vad32m/OpenDcLoad/hw/analog_sim/load_frontend.cir

[Main]
FileType=CIR
Version=12.00
Program=Micro-Cap
Component Version=10.00
Shape Version=11.00
Screen=1680,1050
MCAPVersion=12.2.0.3
Key ID=Demo
NLCnt=155
TXCnt=8

[shapedef]
Name=Animated SPDT Switch
Animated SPDT Switch=0,0,48,16
Current=0,24,16,24
Current=0,-8,16,-8
Current=32,0,48,0

[shapedef]
Name=Animated SPST Switch
Animated SPST Switch=0,-8,48,8
Current=16,8,32,8

[shapedef]
Name=Comp6
Root="Plus.root",9,-12,0
Root="Minus.root",9,44,0
Line=16,48,16,26
Line=16,-16,16,5
Line=24,21,24,40
Line=24,40,56,40
Root="Opamp.root",-16,-8,0

[shapedef]
Name=DNMOS
Root="Mos2.root",0,0,0
Line=14,0,24,0
PolyClosed=3
PolyLine=17,0
PolyLine=20,-3
PolyLine=20,3

[shapedef]
Name=Ground
Line=0,0,12,0
Line=12,-8,12,8
Line=18,-4,18,4
Line=24,0,24,0

[shapedef]
Name=Minus.root
Line=-2,0,2,0

[shapedef]
Name=Mos2.root
Line=0,8,10,8
Line=10,-8,10,8
Line=14,-11,14,-5
Line=14,-3,14,3
Line=14,5,14,11
Line=14,-8,24,-8
Line=14,8,24,8
Line=24,0,24,24
Line=24,-8,24,-24
Current=32,-24,32,-16
Current=32,24,32,16
Current=0,0,8,0

[shapedef]
Name=Opamp5
Root="Opamp.root",0,0,0
Root="Plus.root",25,-4,0
Root="Minus.root",25,52,0
Line=32,56,32,34
Line=32,-8,32,13

[shapedef]
Name=Opamp.root
Line=0,48,6,48
Line=0,0,5,0
Line=6,-4,6,52
Line=6,-4,48,24
Line=6,52,48,24
Line=48,24,72,24
Line=10,12,14,12
Line=12,10,12,14
Line=10,36,14,36
Line=4,0,6,0

[shapedef]
Name=Plus.root
Line=-2,0,2,0
Line=0,-2,0,2

[shapedef]
Name=Pot
Line=0,0,12,0
Line=12,0,14,-4
Line=14,-4,18,4
Line=18,4,22,-4
Line=22,-4,26,4
Line=26,4,30,-4
Line=30,-4,34,4
Line=34,4,36,0
Line=36,0,48,0
PolyClosed=4
PolyLine=24,4
PolyLine=24,4
PolyLine=22,8
PolyLine=26,8
Line=24,8,24,16

[shapedef]
Name=Resistor
PolyOpen=12
PolyLine=0,0
PolyLine=0,0
PolyLine=12,0
PolyLine=14,-4
PolyLine=18,4
PolyLine=22,-4
PolyLine=26,4
PolyLine=30,-4
PolyLine=34,4
PolyLine=36,0
PolyLine=48,0
PolyLine=48,0
Current=32,8,16,8

[shapedef]
Name=SPICE_V
Root="Vsource.root",0,0,0

[shapedef]
Name=Tie
Line=0,0,7,0
Line=7,-8,7,8

[shapedef]
Name=Vsource.root
Line=0,0,12,0
Line=36,0,48,0
Ellipse=12,-12,36,12
FColor=None
Line=7,5,7,9
Root="Plus.root",41,7,0
Current=32,16,16,16

[compdef]
Name=Resistor
Definition=Resistor
Shape=Resistor
Mask=6913
Used=170
memo=Resistor
Label Offset=18,6,8,11
PinCnt=2
Pin="Plus",6,0,-10,-4
Pin="Minus",0,0,-14,-4

[compdef]
Name=Ground
Definition=Ground
Shape=Ground
Mask=1793
Used=277
memo=Ground
Label Offset=0,0,0,0
PinCnt=1
Pin="PinA",0,0,-3,-7

[compdef]
Name=Voltage Source
Definition=VSpice
Shape=SPICE_V
Mask=4865
Used=41
memo=Voltage Source
Label Offset=19,13,15,13
PinCnt=2
Pin="Plus",6,0,-5,-6
Pin="Minus",0,0,-20,-6

[compdef]
Name=Tie
Definition=Tie
Shape=Tie
Mask=5632
Used=9
memo=Ties two nodes together
Label Offset=11,-6,-6,8
PinCnt=1
Pin="PinA",0,0,-7,-9

[compdef]
Name=IRFP350
Definition=NMOS
Shape=DNMOS
Mask=4224
Used=1
memo=N-Channel Power MOSFET Vdss=400V Id=15A Rds=0.3ohm
Label Offset=29,-13,-5,26
PinCnt=4
Pin="Drain",3,-3,7,8
Pin="Gate",0,1,-19,-2
Pin="Source",3,3,6,12
Pin="Body",3,3,6,0
Power=180

[compdef]
Name=AD8628
Definition=Subckt
Shape=Opamp5
Mask=4224
Used=3
memo=Zero Drift, Single Supply, Rail-to-Rail I/O Opamp
Label Offset=51,31,-10,41
PinCnt=5
Pin="1",a,0,0,-3,-4
Pin="2",a,0,6,-3,18
Pin="99",a,4,-1,6,15
Pin="50",a,4,7,6,0
Pin="45",a,9,3,-3,-3

[compdef]
Name=INA214
Definition=Subckt
Shape=Comp6
Mask=4224
Used=2
memo=Voltage Output, High or Low Side Measurement, Bidirectional Zero Drift Series Current Shunt Monitor Gain=100
Link=http://www.ti.com/lit/ds/symlink/ina210.pdf
Label Offset=27,42,-7,24
PinCnt=6
Pin="IN+",a,-2,-1,-12,0
Pin="IN-",a,-2,5,-12,0
Pin="V+",a,2,-2,5,8
Pin="GND",a,2,6,4,8
Pin="OUT",a,7,2
Pin="REF",a,7,5

[compdef]
Name=Animated SPDT Switch
Definition=ANIMATED SPDT SWITCH
Shape=Animated SPDT Switch
Mask=4096
Used=1
memo=Animated Single Pole, Double Throw Switch
Label Offset=1,22,11,7
PinCnt=3
Pin="A",0,0,4,0
Pin="B",0,2,3,10
Pin="C",6,1,-6,-1

[compdef]
Name=Pot
Definition=Macro
Shape=Pot
Mask=4096
Used=3
memo=Potentiometer Macro
Label Offset=32,4,9,11
PinCnt=3
Pin="PINA",a,0,0,-13,-5
Pin="PINB",a,3,2,6,5
Pin="PINC",a,6,0,-12,-5

[compdef]
Name=Animated SPST Switch
Definition=ANIMATED SPST SWITCH
Shape=Animated SPST Switch
Mask=4352
Used=5
memo=Animated Single Pole, Single Throw Switch
Label Offset=2,5,11,11
PinCnt=2
Pin="A",0,0,5,0
Pin="B",6,0,-10,1

[compdef]
Name=LM6161
Definition=Opamp
Shape=Opamp5
Mask=4224
Used=1
memo=High Speed Opamp
Label Offset=51,32,-15,46
PinCnt=5
Pin="Plus input",0,0,-30,-3
Pin="Minus input",0,6,-36,17
Pin="VEE",4,7,6,5
Pin="Output",9,3,-13,-4
Pin="VCC",4,-1,6,4

[Circuit]
Window Placement=2,3, -1,-1, -8,-30, 0,0,982,365
Default Object=Color=#000080
Default Object Font=Height=-15,FStyle=0,Color=#000080,Name=Arial
Default Object Apply Border To Text=No
Default Object Apply Fill To Text=No
Default Object GridSnap=No
NodeVoltageFormat=3
CurrentFormat=3
PowerFormat=3
PathDelayFormat=3
WarningFormat=3
GridTextFormulaFormat=3
Window Placement in Transient Analysis=3,3, 0,780, -8,-30, 125,125,1307,475
Window Placement in Transient Probe=0,1, -1,-1, -8,-30, 676,0,1352,521
Window Placement in AC Analysis=2,3, -1,-1, -8,-30, 25,25,1207,409
Window Placement in AC Probe=0,1, -1,-1, -8,-30, 676,0,1352,521
Window Placement in DC Analysis=2,3, -1,-1, -8,-30, 25,25,1207,375
Window Placement in DC Probe=0,1, -1,-1, -8,-30, 676,0,1352,521
SpiceType=AMBIGUOUS
Title_Block_Border=None
Title_Block=False
Show Nodes=False
Show Voltages=False
Show Current=False
Show Power=False
Show Condition=False
Show Pin Connections=False
Show Connection Warnings=False
Show Cross=False
Show Attribute Text=True
Show Grid Text=True

[Comp]
Name=Resistor
Px=1216,704
Rot=3

[Attr]
ON=-24,-25,PART
V=R1
Style=8192

[Attr]
ON=-43,-39,RESISTANCE
V=0.01
Style=8192

[Attr]
ON=0,0,PACKAGE
V

[Comp]
Name=Ground
Px=1216,736
Rot=7

[Comp]
Name=Ground
Px=624,464
Rot=7

[Comp]
Name=Voltage Source
Px=1536,408
Rot=3

[Attr]
ON=-31,-27,PART
V=V1
Style=8192

[Attr]
ON=-80,-41,VALUE
V=DC 5 AC 0 0

[Attr]
ON=0,0,PACKAGE
V

[Attr]
ON=0,0,SMOOTHING
V=N
Style=256

[Attr]
ON=0,0,Saved_PulseS
V=N
Style=256

[Attr]
ON=0,0,FRACTION
V=.2
Style=256

[Attr]
ON=0,0,Saved_PulseF
V=.2
Style=256

[Attr]
ON=0,0,Saved_Pulse
V=DC 0 AC 1 0 Pulse 0 5 100n 10n 10n 400n 1u
Style=256

[Attr]
ON=0,0,Saved_None
V=DC 5 AC 0 0
Style=256

[Comp]
Name=Tie
Px=624,376
Rot=5

[Attr]
ON=-25,-30,PART
V=VCC_DAC
Style=8192

[Comp]
Name=Tie
Px=1120,376
Rot=5

[Attr]
ON=-22,-26,PART
V=VCC_12
Style=8192

[Wire]
Pxs=1536,336,1536,360

[Comp]
Name=Ground
Px=1120,472
Rot=7

[Comp]
Name=IRFP350
Px=1192,432

[Attr]
ON=29,-13,PART
V=M2
Style=8192

[Attr]
ON=29,1,MODEL
V=IRFP350

[Attr]
ON=29,15,POWER
V=180

[Attr]
ON=29,43,PACKAGE
V=TO-247AC

[Wire]
Pxs=1216,704,1216,736

[Comp]
Name=AD8628
Px=1080,872
Rot=6

[Attr]
ON=-66,31,PART
V=X3
Style=8192

[Attr]
ON=-51,45,NAME
V=AD8628

[Attr]
ON=-51,73,PACKAGE
V=SOIC8

[Comp]
Name=INA214
Px=1064,584
Rot=6

[Attr]
ON=-42,42,PART
V=X4
Style=8192

[Attr]
ON=-27,56,NAME
V=INA214

[Attr]
ON=-27,84,PACKAGE
V=SC70-6

[Comp]
Name=Ground
Px=1096,648
Rot=7

[Comp]
Name=Ground
Px=1048,928
Rot=7

[Wire]
Pxs=1080,920,1112,920

[Wire]
Pxs=1096,624,1096,640

[Wire]
Pxs=1080,576,1144,576

[Wire]
Pxs=1080,872,1144,872

[Wire]
Pxs=1144,616,1216,616

[Wire]
Pxs=1144,616,1144,872

[Wire]
Pxs=1216,616,1216,656

[Wire]
Pxs=1080,624,1096,624

[Wire]
Pxs=1048,632,1048,640

[Wire]
Pxs=1048,640,1096,640

[Wire]
Pxs=1096,640,1096,648

[Comp]
Name=Tie
Px=1048,560
Rot=5

[Attr]
ON=-19,-24,PART
V=VCC_12
Style=8192

[Wire]
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
Style=8192

[Attr]
ON=-34,9,RESISTANCE
V=1.5K
Style=8192

[Attr]
ON=0,0,PACKAGE
V

[Comp]
Name=Ground
Px=768,312
Rot=7

[Wire]
Pxs=552,216,584,216

[Wire]
Pxs=552,216,552,304

[Wire]
Pxs=648,304,688,304

[Wire]
Pxs=688,240,688,304

[Wire]
Pxs=688,304,704,304

[Comp]
Name=Tie
Px=624,168
Rot=5

[Attr]
ON=-15,-26,PART
V=VCC_5
Style=8192

[Wire]
Pxs=552,304,600,304

[Wire]
Pxs=752,304,768,304

[Wire]
Pxs=768,304,768,312

[Comp]
Name=Resistor
Px=968,216
Rot=1

[Attr]
ON=-30,-7,PART
V=R17
Style=8192

[Attr]
ON=-34,9,RESISTANCE
V=56K
Style=8192

[Attr]
ON=0,0,PACKAGE
V

[Comp]
Name=Resistor
Px=968,280
Rot=1

[Attr]
ON=-33,5,PART
V=R18
Style=8192

[Attr]
ON=-34,21,RESISTANCE
V=22K
Style=8192

[Attr]
ON=0,0,PACKAGE
V

[Comp]
Name=Ground
Px=968,328
Rot=7

[Wire]
Pxs=1160,208,1216,208

[Wire]
Pxs=1216,208,1216,408

[Wire]
Pxs=968,208,1096,208

[Wire]
Pxs=968,264,968,272

[Wire]
Pxs=968,208,968,216

[Wire]
Pxs=872,272,872,280

[Wire]
Pxs=872,272,968,272

[Wire]
Pxs=968,272,968,280

[Wire]
Pxs=1096,208,1112,208

[Wire]
Pxs=872,192,872,272

[Comp]
Name=Resistor
Px=808,192
Rot=2

[Attr]
ON=-30,-23,PART
V=R19
Style=8192

[Attr]
ON=-34,9,RESISTANCE
V=100K
Style=8192

[Attr]
ON=0,0,PACKAGE
V

[Wire]
Pxs=656,192,760,192

[Wire]
Pxs=808,192,872,192

[Comp]
Name=Resistor
Px=472,240
Rot=1

[Attr]
ON=-30,-7,PART
V=R20
Style=8192

[Attr]
ON=-34,9,RESISTANCE
V=180K
Style=8192

[Attr]
ON=0,0,PACKAGE
V

[Comp]
Name=Resistor
Px=472,320
Rot=1

[Attr]
ON=-30,-7,PART
V=R21
Style=8192

[Attr]
ON=-34,9,RESISTANCE
V=120K
Style=8192

[Attr]
ON=0,0,PACKAGE
V

[Comp]
Name=Ground
Px=472,392
Rot=7

[Wire]
Pxs=472,216,472,240

[Wire]
Pxs=472,216,552,216

[Wire]
Pxs=472,288,472,320

[Wire]
Pxs=472,368,472,392

[Grid Text]
Text="OPAx189"
Px=1136,416
GridSnap=True
JustifyH=Left
JustifyV=Bottom
CBorder=None

[Grid Text]
Text="10 A = 10 V"
Text="1 A = 1 V"
Px=968,592
GridSnap=True
JustifyH=Left
JustifyV=Bottom
CBorder=None

[Grid Text]
Text="Gain = 10"
Text="10 mV -> 100 mV"
Text="10 uV  -> 100 uV"
Px=920,888
GridSnap=True
JustifyH=Left
JustifyV=Bottom
CBorder=None

[Grid Text]
Text="1 mA = 10 uV"
Text="10 mA = 100 uV"
Text="1 A = 10 mV"
Text="10 A = 100 mV"
Text=""
Text="Low current: AD8628 / OPA2189"
Text="High current: INA293x3"
Px=1248,672
GridSnap=True
JustifyH=Left
JustifyV=Bottom
CBorder=None

[Grid Text]
Text="Gain = 19.9"
Text="100 mV -> 1.99 V"
Text="100 uV ->  1.99 mv"
Px=648,888
GridSnap=True
JustifyH=Left
JustifyV=Bottom
CBorder=None

[Grid Text]
Text="Gain = 25"
Text="10 V -> 202 mV -> 5 V"
Text="10 mV -> 202 uV -> 5 mV"
Px=392,192
GridSnap=True
JustifyH=Left
JustifyV=Bottom
CBorder=None

[Grid Text]
Text="Gain = 0.02016"
Text="350 V -> 7.06 V"
Text="100 V ->  2.02 V"
Text="1 V -> 20.2 mV"
Text="10 mV -> 202 uV"
Px=1064,208
GridSnap=True
JustifyH=Left
JustifyV=Bottom
CBorder=None

[Grid Text]
Text="Gain = 0.28"
Text="350 V -> 7.06 V -> 1.98 V"
Text="1 V -> 20.2 mV -> 5.66 mV"
Text="100 mV -> 2.02 mV -> 566 uV"
Px=888,400
GridSnap=True
JustifyH=Left
JustifyV=Bottom
CBorder=None

[Schematic]
CurrentSection 0=0
CurrentSection 1=0
CurrentSection 2=0
CurrentSection 3=0
Splitter.xs=0
Splitter.ys=0
TextQuad=4099
Scale=1
GridType=Normal
GridUser=10
ShapeGroups="Main","Euro","Polarity","Main1","Main11","Electrolytic","GroundArrow","DeMorgan"
CalcRMS=False
CalcAVG=False
CalcPeak=False
CalcVoltage=True
DisplayMeasure=Last
ShareScales=True

[Tools]
Pos=Top
FILESAVEASOLD=No
BOM=No
FILEPCB=No
PROBE=Yes
SELECT=Yes
PAN=Yes
COMP=Yes
TEXT=Yes
WIRE=Yes
WIRED=Yes
BUS=Yes
GRAPHIC=Yes
FLOWCHART=Yes
LINE=No
ELLIPSE=No
RECT=No
DIAM=No
ARC=No
PIE=No
TRIANGLE=No
STAR=No
LEFTBRK=No
RIGHTBRK=No
BOTHBRK=No
META=No
PARALLELOGRAM=No
FC_PROCESS=No
FC_ALT_PROCESS=No
FC_DECISION=No
FC_DATA=No
FC_PREDEFPROCESS=No
FC_INTERNALSTORAGE=No
FC_DOCUMENT=No
FC_MULTIDOCUMENT=No
FC_TERMINATOR=No
FC_PREPARATION=No
FC_MANUALINPUT=No
FC_MANUALOPERATION=No
FC_CONNECTOR=No
FC_OFFPAGECONNECTOR=No
FC_PUNCHCARD=No
FC_PUNCHEDTAPE=No
FC_SUMMING_JUNCTION=No
FC_OR=No
FC_COLLATE=No
FC_SORT=No
FC_EXTRACT=No
FC_MERGE=No
FC_STORED_DATA=No
FC_DELAY=No
FC_SAS=No
FC_MAGNETIC_DISK=No
FC_DAS=No
FC_DISPLAY=No
SPREAD_SHEET=Yes
POLYCLOS=No
POLYOPEN=No
FLAG=Yes
INFO=Yes
HELP=Yes
HELP_SPICE=No
LINK=Yes
CHECK=Yes
REGION_ENABLE=Yes
TITLE_BLOCK=Yes
DIGTRC=No
DIGTRC2=No
BUILD_COMMAND=Yes
DIGALL=No
GRIDTEXT=Yes
COMPTEXT=Yes
NODE=Yes
MEASURED=Yes
NODEV=Yes
CURRENT=Yes
POWER=Yes
CONDITIN=Yes
PIN=Yes
CONNWARN=Yes
CROSS=No
GRID=Yes
BORDER=Yes
BORDERONE=Yes
TITLE=Yes
RUBBER=Yes
PROPERTY=Yes
STEP=Yes
MIRROR=Yes
ROTATE=Yes
FLIPY=Yes
FLIPX=Yes
CIR_MAKEMACRO=No
CLEARCUTWIRE=No
CLIPBOARDCIRPAGE2BMM=No
FINDCOMP=Yes
FIND=Yes
REPEAT=No
REPLACE=No
MODEL=Yes
CIR2CKT=No
ATTDISP=No
ENABLE=Yes
DISABLE=Yes
ENABLE_WITH=Yes
TOFRONT=Yes
TOBACK=Yes
SELNEXT=No
PAGEADD=No
PAGEADDTEXT=No
ADDSECTION=No
PAGEDEL=No
ZOOMIN=Yes
ZOOMOUT=Yes
AUTOSCALECIR=Yes
GOTOFLAG=No
UPLEVEL=Yes
COLOR=Yes
FONT=Yes
STYLE=Yes
DM_LAST=No
DM_RMS=No
DM_AVG=No
DM_PEAK=No
GRID_NONE=No
GRID_NORMAL=No
GRID_BOLD_5=No
GRID_BOLD_6=No
GRID_BOLD_USER=No
GRAPH_PAPER=No
SPLITCIRTEXTH=No
SPLITCIRTEXTV=No
SPACE_SPLITTERS_EVENLY=No
NORMALCIR=No
RENAMEDEFINE=No
RENAMECMP=No
ATTALIGN=No
RESETNODEPOS=No
FIT2STANDARD=No
NODESNAP=No
MOVETEXT=No
TEXTINC=No
TOGGLETEXT=No
TOGGLEMODE=No
TOLERANCE=No
ALIGNAB=No
ALIGNLEFT=No
ALIGNCENTER=No
ALIGNRIGHT=No
ALIGNTOP=No
ALIGNMIDDLES=No
ALIGNBOTTOM=No

[Section]
Index=0
Name="load_frontend"
Type=Main
Enable=True
CurrentPage 0=0
CurrentPage 1=0
CurrentPage 2=0
CurrentPage 3=0
TabSize 0=425
TabSize 1=425
TabSize 2=425
TabSize 3=425

[Page]
Index=0
Section=0
Print=True
Enable=True
Name=Main
PrinterScale=1
Scale 0=1
Scale 1=1
Scale 2=1
SB 3=317,52
Scale 3=1
Px=510,457
WinBackGround Color=#FFFFFF
Select Color=#FF0000
Anchor Color=#000000
Select Box Color=#000080
Grid Text Color=Height=-12,FStyle=0,Color=#0000FF,Name=Verdana
Grid Text RTF=False
Grid Text Angle=0
Grid Text GridSnap=True
Grid Text PinIt=False
Grid Text JustifyH=Left
Grid Text JustifyV=Bottom
Grid GradientColor2=None
Grid OutlineThickness=1
Grid OutlineColor=None
Component Color=#0000FF
Attribute Text=Height=-12,FStyle=0,Color=#008000,Name=Verdana
Wire Color=#008000
Bus Color=#008000
Pin Connection=Height=-10,FStyle=0,Color=#FF0000,Name=Arial
Pin Marker Color=#008000
Node Number=Height=-11,FStyle=0,Color=#FF00FF,Name=Arial
Node Voltage Color=Height=-11,FStyle=0,Color=#000000,Name=Arial
Dynamic AC Voltage Color=#E4E4E4
Text Banner Text=Height=-15,FStyle=0,Color=#800000,Name=Arial
Title Block Background=#C0C0C0
Current=Height=-11,FStyle=0,Color=#0000FF,Name=Arial
Power/Condition=Height=-11,FStyle=0,Color=#FF0000,Name=Arial
Digital Path Color=#FF0000
Title Block Border=#000000
Disabled	Color=#C0C0C0
Search Color=#FFFF00
Grid Color=#000000
Graph Paper=#E4E4E4
Digital 0 Color=#000000
Digital R Color=#FFFF00
Digital F Color=#FFFF00
Digital 1 Color=#FF0000
Digital X Color=#C0C0C0
Digital Z Color=#808080
Block Select Color=#51F998

[Page]
Index=1
Section=0
Type=Text
Print=False
Enable=True
Name=Text
Font=Height=-15,FStyle=0,Color=#000000,Name=Courier New
Comment Color=#008000
WinBackGround Color=#FFFFFF
Disabled	Color=#C0C0C0
KeyWord Color=#0000FF
Error	Color=#FF0000
Search Color=#FFFF00

[Page]
Index=2
Section=0
Type=Text
Print=False
Enable=True
Name=Models
Font=Height=-15,FStyle=0,Color=#000000,Name=Courier New
Comment Color=#008000
WinBackGround Color=#FFFFFF
Disabled	Color=#C0C0C0
KeyWord Color=#0000FF
Error	Color=#FF0000
Search Color=#FFFF00

[Page]
Index=3
Section=0
Type=Info
Print=False
Enable=True
Name=Info
Font=Height=-15,FStyle=0,Color=#000000,Name=Courier New
Comment Color=#008000
WinBackGround Color=#FFFFFF
Disabled	Color=#C0C0C0
KeyWord Color=#0000FF
Error	Color=#FF0000
Search Color=#FFFF00

[Text Area]
Section=0
Page=1
Text=.OPTIONS ITL1=250
Text=.OPTIONS PIVREL=1
Text=.OPTIONS ITL4=50

[Text Area]
Section=0
Page=2
Text=
Text=.MODEL REPEATER OPA ()
Text=.MODEL OPAMP OPA (GBW=10MEG VEE=0 VNS=0 VOFF=50u)

[InfoPage]
InfoPage=True
Warnings=True
System=True
Defines=True
Array=True
Model=True
Measure=True
MacroSubckt=True
NotUsed=True
ComponentCounts=True
VariablizePaths=False
DontShowPaths=False
SimulationLog=True

[Transient]
WinID=1
Window Placement=3,3, 0,780, -8,-30, 125,125,1307,475
Font=Height=-19,FStyle=0,Color=#0000FF,Name=Arial
WinBackGround Color=#FFFFFF
Select Color=#FF0000
Anchor Color=#000000
Select Box Color=#000080
Window Placement in Probe=0,1, -1,-1, 0,0, 0,0,676,521
Title=load_frontend.cir
AutoTitle=Yes
Grid Color=#808080
Grid Weight=1
Grid Pattern=Dot6
Tracker Foreground=Height=-15,FStyle=0,Color=#000000,Name=Arial
Tracker Background=#FFFF00
Baseline color=#0000FF
BaseLine Weight=1
CurveFit color=#FF0000
CurveFit Weight=2
CurveFit Pattern=Dash
Static Grids=False
PlusMark=False
MinorLog25=Off
LabelMinor=Off
DataPoints=False
Token=False
Ruler=False
XAxisGrids=True
YAxisGrids=True
MinorLogGrids=True
BaseLine=False
AlignZ=True
Align Cursors=True
TagFormatX=3
TagFormatY=3
FormulaFormat=2
EndMode=SCALE
Graph Background=#FFFFFF
Tracker Intercept=False
Tracker Mouse=True
Tracker Cursor=True
Tracker Cursor BranchInfo=False
Horizontal Cursor=False
Same Y Scales=Yes
Enable X Scaling=True
Enable Y Scaling=True
Keep X Scales The Same=True
Number of Grids X=5
Number of Grids Y=5
Cursor Select Color Primary=#C0C0C0
Cursor Select Color Secondary=#FF0000
Data Point Labels Color Fore=Height=-15,FStyle=0,Color=#000000,Name=Arial
Data Point Labels Color Back=#FFFF00
OperPoint=True
OperPointOnly=False
AutoScaleRanges=True
FixedTimeStep=False
DoPSS=False
PSS_Periods="1"
PSS_Iterations="5"
PSS_Error="1u"
PSS_ShowPlots=True
FFT_NPts="8192"
FFT_IncludeDCHarmonic=False
FFT_AutoScale_Harmonics="10"
PrinterAutoTile=No
PrinterBlackBorder=No
MonMaxShow=4
MonPageWidth=66
MonPlotWidth=21
MonExprXWidth=142
MonExprYWidth=367
MonRangeXWidth=90
MonRangeYWidth=90
AnimateWait=None
AnimateWaitTime=500
AnimatePressAfter=0
Save_For_Future=No
Reduce_Display=1
Reduce_Save=1
Reduce_ThrowDataOut=0
Num Out Header Left
Num Out Header Center="$MC\n$user\n$company\n$Analysis of $name\n$date $time"
Num Out Header Right
Num Out Delimiter=32
Num Out Write=True
Num Out Write Main Header=True
Num Out Write Limits=True
Num Out Write Branch Header=True
Num Out Write Models=False
Num Out Write Zero Models=True
Num Out Write Undefined Models=True
Num Out Write Operating Point=True
Num Out Write Measurement Values=True
Num Out Write Tolerance Detail=True
Num Out Write Values=True
Num Out Write Waveform Header=True
Num Out Allow Dup Y Expr=False
Num Out Low="TSTART"
Num Out High="TMAX"
Num Out Font=Height=-15,FStyle=0,Color=#000000,Name=Courier New
Num Out Format=3
Num Out HideNonSelected=False
Num Out UseActualDataPoints=False
AutoSaveWave=False
Wave Format=16E
State Variables Format=5E
Print Individual Pages=False

[Tools]
Pos=Top
SELECT=Yes
PAN=Yes
GRAPHIC=Yes
LINE=No
ELLIPSE=No
RECT=No
DIAM=No
ARC=No
PIE=No
TRIANGLE=No
STAR=No
LEFTBRK=No
RIGHTBRK=No
BOTHBRK=No
META=No
PARALLELOGRAM=No
POLYCLOS=No
POLYOPEN=No
SCALE=Yes
CURSOR=Yes
MEASUREH=Yes
MEASUREV=Yes
TAG=Yes
PTAG=Yes
TEXT=Yes
PROPERTY=Yes
START=Yes
STOP=Yes
PAUSE=Yes
RESUME=No
DATAPTS=Yes
TOKENS=Yes
RULER=Yes
PLUS=Yes
XAXIS=Yes
YAXIS=Yes
MINORLOG=Yes
LOG25=Yes
BASELINE=Yes
HORIZCUR=Yes
GOTOX=Yes
GOTOY=Yes
GOTOPERF=Yes
GOTOBRNC=Yes
CLEAR_ACCUMULATED=Yes
PDELETE_ALL_PLOTS=Yes
NEXT=Yes
NEXTIN=Yes
PEAK=Yes
VALLEY=Yes
HIGH=Yes
LOW=Yes
INFLECTN=Yes
GHIGH=Yes
GLOW=Yes
BOTTOM=Yes
TOP=Yes
WAVEFORMBUFFER=Yes
AOUTPUT=Yes
PKEY=Yes
ENXSCALE=Yes
ENYSCALE=Yes
ZOOMIN=Yes
ZOOMOUT=Yes
AUTOSCALE=Yes
RESTORESCALE=No
COLOR=Yes
FONT=Yes
STYLE=Yes
SELNEXT=No
NORMALIZE=No
NORMALIZE_MIN=No
NORMALIZE_MAX=No
ADD_TAG_LEFT=No
ADD_TAG_RIGHT=No
ADD_HORZ_TAG=No
ADD_VERT_TAG=No
ALIGN_CURSORS=No
ALIGN_CURSORSZ=No
CURSORTOCLIPBOARD=No
TRACKER_CURSOR=No
TRACKER_CURSOR_BRANCHINFO=No
TRACKER_INTERCEPT=No
TRACKER_MOUSE=No
TOFRONT=Yes
TOBACK=Yes
SPLITCIRTEXTH=No
SPLITCIRTEXTV=No
SPACE_SPLITTERS_EVENLY=No
NORMALCIR=No
LABEL_WAVEFORM=No
LABEL_DATA_POINTS=No
WFB_ADD_TO_LIMITS=No
ENVELOPE=No
SAMEYSCALES=No
KEEPXSCALESTHESAME=No
CURVEFIT=No
ADD_MARKER=No
SHOWWATCH=No
BP=No
TOGGLEMODE=No
REMOVEALLTEXT=No
AUTOSCALEX=No
LABELALLMINOR=No
ALIGNLEFT=No
ALIGNCENTER=No
ALIGNRIGHT=No
ALIGNTOP=No
ALIGNMIDDLES=No
ALIGNBOTTOM=No

[APage]
Analysis=Transient
Name="MAIN"

[AObject]
Analysis=Transient
Object=MeasureH
Locked=True
EndPoint=ArrowF
CBorder=#000080
w=1
AliasID1=2
w2=1
AliasID2=2
Pos=0.021053762222738588,0.66943273897760336,0.02452781442202508,0.66897883189309126
Posm=0.66601562500000011
Font=Height=-15,FStyle=0,Color=#FF0000,Name=Arial
Format=3

[AObject]
Analysis=Transient
Object=MeasureH
Locked=True
EndPoint=ArrowF
CBorder=#000080
w=1
AliasID1=2
w2=1
AliasID2=2
Pos=0.014376057165613482,0.67046238780486944,0.017770676247238496,0.67021067056269401
Posm=0.66679687500000007
Font=Height=-15,FStyle=0,Color=#FF0000,Name=Arial
Format=3

[AObject]
Analysis=Transient
Object=Tag
Locked=True
EndPoint=ArrowF
CBorder=#000080
w=0
AliasID1=1
Pos=0.044589853958713864,2.7269567936677954,0.028805620608899296,4.3084577114427871
Font=Height=-15,FStyle=0,Color=#0000FF,Name=Arial
Format=3
FormatY=3
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
