vad32m/OpenDcLoad/src/error_codes.h

/**
 * @file Description of error codes
 */

#ifndef SRC_ERROR_CODES_H_
#define SRC_ERROR_CODES_H_

/**
 * No error occured
 */
#define ERR_OK         (0)

/**
 * Allocation error
 */
#define ERR_NOMEM     (-1)

/**
 * Invalid argument
 */
#define ERR_INARG     (-2)

#endif /* SRC_ERROR_CODES_H_ */
