vad32m/OpenDcLoad/src/platform/display_connection.h

#ifndef __LCD_CONNECTION__
#define __LCD_CONNECTION__

#include <stdint.h>

typedef void (*xfer_completed_cb)(void);

int32_t
display_connection_init(void);

void
display_connection_write_cmd(uint8_t cmd);

void
display_connection_write_data(uint8_t data);

void
display_connection_write_data_16(uint16_t data);

uint8_t
display_connection_read_data(void);

void
display_connection_duplicate_data(uint16_t number, uint32_t repetitions, xfer_completed_cb callback);

void
display_connection_write_data_bulk(uint16_t* data, uint32_t data_count, xfer_completed_cb callback);

#endif //__LCD_CONNECTION__
