vad32m/OpenDcLoad/src/ui/views/mode_select_view.c

#include "ui/views/mode_select_view.h"
#include "ui/views/mode_select_view_layout.h"
#include "ui/views/lvgl_view.h"
#include "lvgl.h"

#include "debug/assertions.h"
#include "error_codes.h"

#include <stdlib.h>

#define MODE_SELECT_BUF_SIZE 120
#define MAX_NUMBER_OF_LIST_ITEMS 5
#define UI_MODES_LIST_LINES 6

typedef struct mode_select_view_pvt_data_struct {
    lv_obj_t* list;
    char lvgl_list_text[MODE_SELECT_BUF_SIZE];
    uint8_t index_map[MAX_NUMBER_OF_LIST_ITEMS];
} mode_select_view_pvt_data_t;

int32_t mode_select_view_init(mode_select_view_t* view_to_init)
{
    ASSERT_PTR_VALID(view_to_init);

    lvgl_basic_view_create(&view_to_init->view);
    lv_obj_t* screen = lvgl_basic_view_get_screen(view_to_init);
    mode_select_view_pvt_data_t* view_data = malloc(sizeof(mode_select_view_pvt_data_t));

    ASSERT_NON_NULL(view_data);

    if (view_data) {
        view_to_init->pvt_data = view_data;
        view_data->list = lv_roller_create(screen, NULL);
        lv_obj_set_pos(view_data->list, UI_MODES_LIST_X_POS, UI_MODES_LIST_Y_POS);
        lv_obj_set_size(view_data->list, UI_MODES_LIST_WIDTH, UI_MODES_LIST_HEIGHT);
        lv_roller_set_fix_width(view_data->list, UI_MODES_LIST_WIDTH);
        lv_roller_set_visible_row_count(view_data->list, UI_MODES_LIST_LINES);
        return ERR_OK;
    }

    return ERR_NOMEM;

}

int32_t mode_select_view_set_modes_list(mode_select_view_t* view,
            mode_select_view_list_item_t* modes, uint8_t modes_num)
{
    ASSERT_PTR_VALID(view);

    mode_select_view_pvt_data_t* view_data = view->pvt_data;

    ASSERT_PTR_VALID(modes);

    if (modes_num > MAX_NUMBER_OF_LIST_ITEMS) {
        return ERR_INARG;
    }

    view_data->lvgl_list_text[0] = '\0';

    for (uint8_t i = 0; i < modes_num; i++) {
        //TODO: make SAFE copy
        strcat(view_data->lvgl_list_text, modes[i].text);
        strcat(view_data->lvgl_list_text, "\n");
        view_data->index_map[i] = modes[i].id;
    }

    lv_roller_set_options(view_data->list, view_data->lvgl_list_text, LV_ROLLER_MODE_NORMAL);
    return ERR_OK;
}


int32_t mode_select_view_set_selected_mode(mode_select_view_t* view, uint8_t id)
{
    ASSERT_PTR_VALID(view);

    mode_select_view_pvt_data_t* view_data = view->pvt_data;

    //TODO: check max number against REAL amount of list items
    for (uint8_t i = 0; i < MAX_NUMBER_OF_LIST_ITEMS; i++) {
        if (view_data->index_map[i] == id) {
            lv_roller_set_selected(view_data->list, i, LV_ANIM_OFF);
            return ERR_OK;
        }
    }

    return ERR_INARG;
}

uint8_t mode_select_view_get_selected_mode(mode_select_view_t* view)
{
    ASSERT_PTR_VALID(view);

    mode_select_view_pvt_data_t* view_data = view->pvt_data;
    return view_data->index_map[lv_roller_get_selected(view_data->list)];
}

void mode_select_view_destroy(mode_select_view_t* view_to_destroy)
{
    ASSERT_PTR_VALID(view_to_destroy);
    mode_select_view_pvt_data_t* view_data = view_to_destroy->pvt_data;
    lv_obj_del(view_data->list);
    free(view_to_destroy);
    lvgl_basic_view_destroy((ui_view_t*)view_to_destroy);
}
