vad32m/OpenDcLoad/src/ui/views/mode_select_view_layout.h

/**
 * Coordinates for UI elements of mode select screen
 */
#ifndef SRC_UI_VIEWS_MODE_SELECT_VIEW_LAYOUT_H_
#define SRC_UI_VIEWS_MODE_SELECT_VIEW_LAYOUT_H_

/*
+ ---------------------------------------------------------------------------+
|                                                                            |
|                                                                            |
|      +-------------------------------------------------------------+------ |
|      |(30,30)                                                      |     ^ |
|      |                                                             |     | |
|      |                                                             |     | |
|      |                                                             |     | |
|      |                                                             |     | |
|      |                                                             |     | |
|      |                                                             |     | |
|      |                     List of modes                           |  250| |
|      |                                                             |     | |
|      |                                                             |     | |
|      |                                                             |     | |
|      |                                                             |     | |
|      |                                                             |     | |
|      |                                                             |     v |
|      +-------------------------------------------------------------------- |
|      |                                                             |       |
|      |                         420                                 |       |
|      |<----------------------------------------------------------->|       |
+----------------------------------------------------------------------------+
|                                                                            |
|                               Buttons                                      |
|                                                                            |
+----------------------------------------------------------------------------+
*/

#define UI_MODES_LIST_X_POS 30
#define UI_MODES_LIST_Y_POS 30

#define UI_MODES_LIST_HEIGHT 250
#define UI_MODES_LIST_WIDTH  420

#endif /* SRC_UI_VIEWS_MODE_SELECT_VIEW_LAYOUT_H_ */
