vad32m/OpenDcLoad/src/ui/views/plot_view_layout.h

/**
 * Coordinates for UI elements of plot view
 */

#ifndef SRC_UI_VIEWS_PLOT_VIEW_LAYOUT_H_
#define SRC_UI_VIEWS_PLOT_VIEW_LAYOUT_H_

#include "src/ui/views/basic_view_layout.h"

/*
+----------------------------------------------------------------------------------+
^     |(0,0)                                                                       |
|35   |                                                                            |
v     |                                                                            |
+----------------------------------------------------------------------------------+
      |                                                                            |
      |                                                                            |
      |      +-------------------------------------------------------------+------ |
      |      |(30,50)                                                      |     ^ |
      |      |                                                             |     | |
      |      |                                                             |     | |
      |      |                                                             |     | |
      |      |                                                             |     | |
      |      |                                                             |  210| |
      |      |                                                             |     | |
      |      |                                                             |     | |
      |      |                                                             |     | |
      |      |                                                             |     v |
      |      +-------------------------------------------------------------------- |
      |      |                                                             |       |
      |      |                         420                                 |       |
      |      |<----------------------------------------------------------->|       |
 +---------------------------------------------------------------------------------+
 ^    |                                                                            |
 |35  |                                                                            |
 v    |                                                                            |
 +----+----------------------------------------------------------------------------+
*/

#define UI_PLOT_X_POS 30
#define UI_PLOT_Y_POS 50

#define UI_PLOT_HEIGTH 210
#define UI_PLOT_WIDTH  420

#endif /* SRC_UI_VIEWS_PLOT_VIEW_LAYOUT_H_ */
