vad32m/OpenDcLoad/src/ui/views/values_view_layout.h

/**
 * Coordinates of UI elements of values view
 */

#ifndef SRC_UI_VIEWS_VALUES_VIEW_LAYOUT_H_
#define SRC_UI_VIEWS_VALUES_VIEW_LAYOUT_H_

/*
+----------------------------------------------------------------------------+
|                                                                            |
|                                                                            |
|     +------------------------+--------------------------------------+      |
|     |(20,20)                 |                                      |      |
|     |                        |                                      |      |
|     +---------------------------------------------------------------+      |
|     |                        |                                      |      |
|     |                        |                                      |      |
|     +---------------------------------------------------------------+      |
|     |                        |                                      |      |
|     |                        |                                      |      |
|     +---------------------------------------------------------------+      |
|     |                        |                                      |      |
|     |                        |                                      |      |
|     +---------------------------------------------------------------+      |
|     |                        |                                      |      |
|     |                        |                                      |      |
|     +---------------------------------------------------------------+      |
|     |                        |                                      |      |
|     |                        |                                      |      |
|     +---------------------------------------------------------------+      |
|     |        100             |                 340                  |      |
|     +<---------------------->+<------------------------------------>+      |
+----------------------------------------------------------------------------+
|                                                                            |
|                               Buttons                                      |
|                                                                            |
+----------------------------------------------------------------------------+

*/

#define UI_VALUES_TABLE_X_POS 20
#define UI_VALUES_TABLE_Y_POS 20

#define UI_VALUES_TABLE_ROWS 6
#define UI_VALUES_TABLE_COLS 2

#define UI_VALUES_TABLE_FIRST_COL_WIDTH 100
#define UI_VALUES_TABLE_SECOND_COL_WIDTH 340

#endif /* SRC_UI_VIEWS_VALUES_VIEW_LAYOUT_H_ */
